jfcbooth/tally/pictures/20211008_170915.jpg

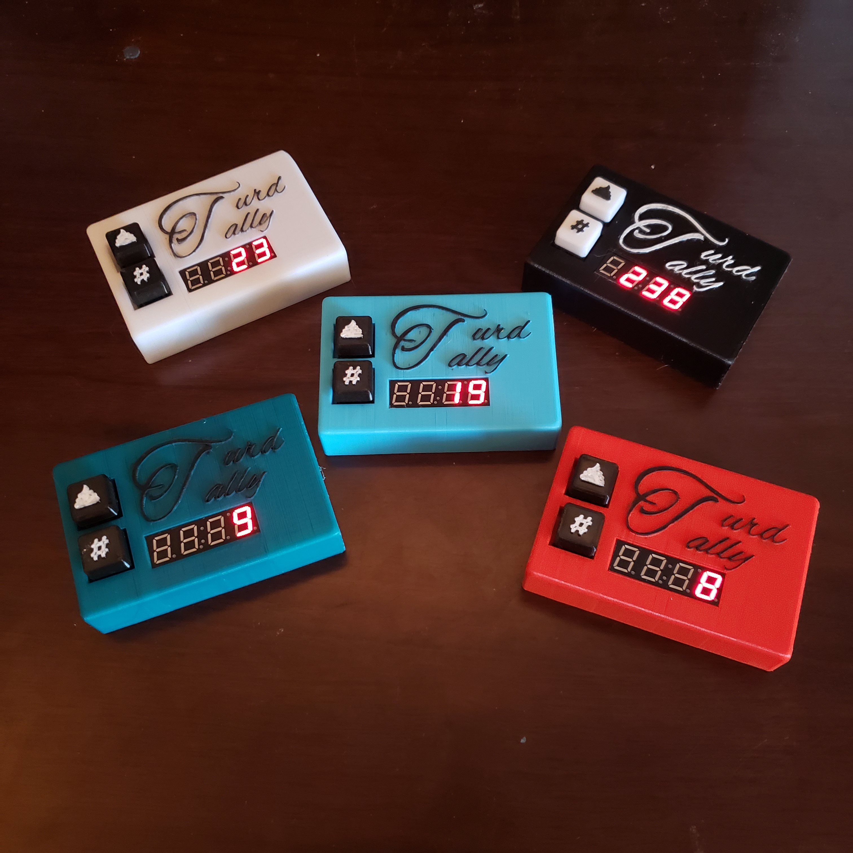
pictures/20211008_170915.jpg
